XasWorks/Notos/Models/Modules/Bumper/FrontBumper.fcstd

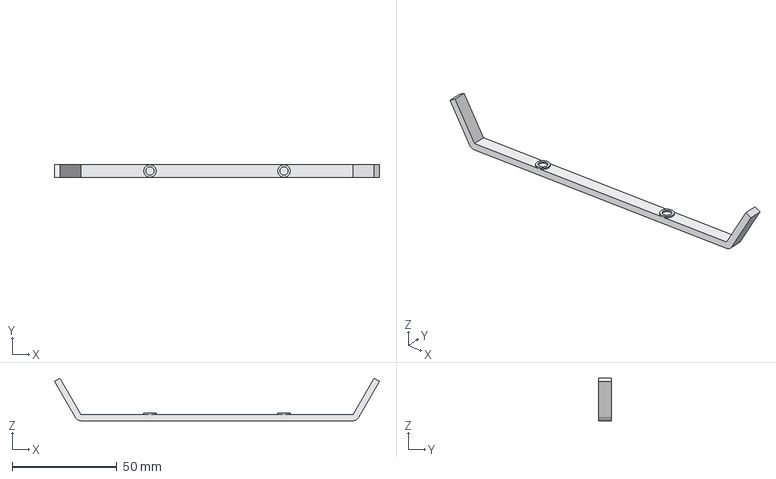
[picture p16: CAD file, 2017-02-04]
Models/Modules/Bumper/FrontBumper.fcstd
155.2 x 6.00 x 20.3 mm
