XasWorks/Notos/Models/BallSearch/Laser Side Mount.fcstd

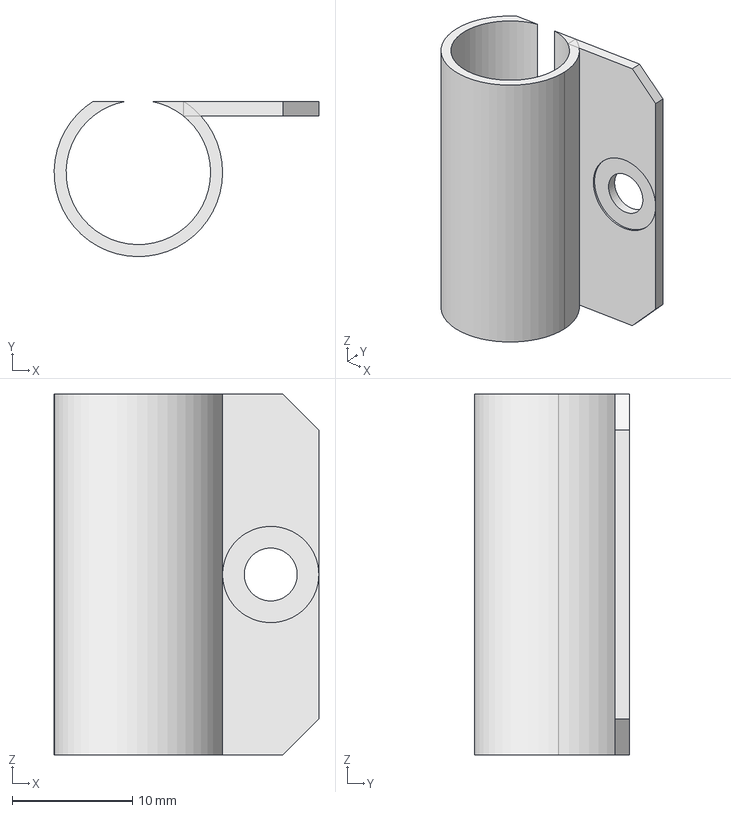
[picture p17: CAD file, 2017-04-10]
Models/BallSearch/Laser Side Mount.fcstd
22.0 x 12.9 x 30.0 mm
