XasWorks/Notos/Models/Modules/MultiSensorMount.fcstd

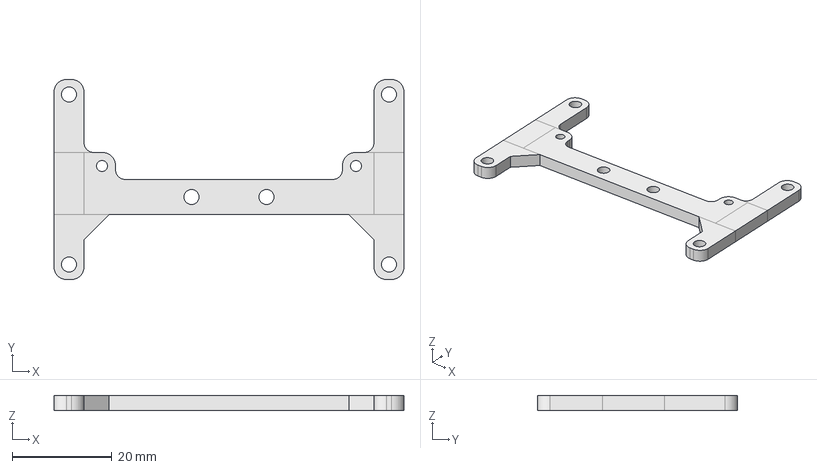
[picture p18: CAD file, 2017-03-13]
Models/Modules/MultiSensorMount.fcstd
70.0 x 40.0 x 3.00 mm
