XasWorks/Notos/Models/BallSearch/PhototransistorCover.fcstd

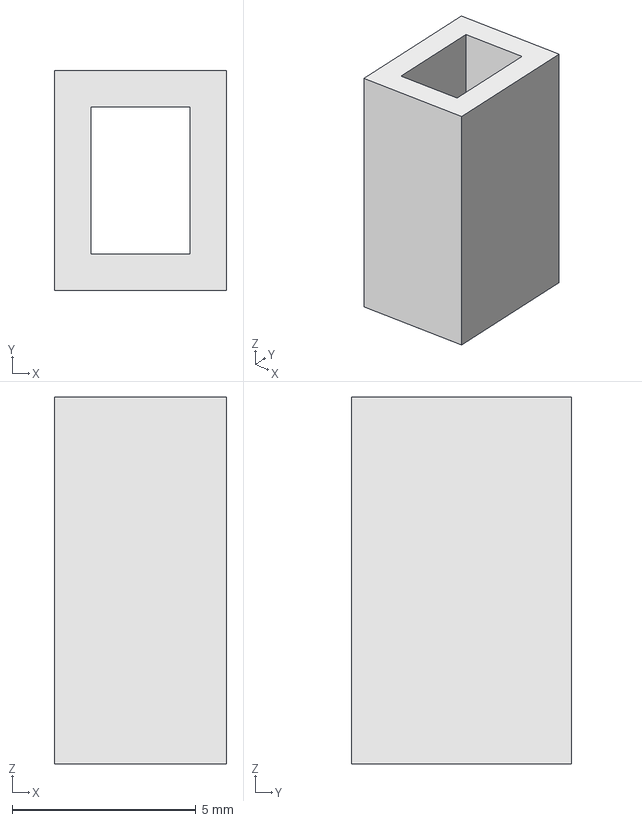
[picture p19: CAD file, 2017-04-10]
Models/BallSearch/PhototransistorCover.fcstd
4.70 x 6.00 x 10.0 mm
