XasWorks/Notos/Models/Modules/GroundDistanceSensor.fcstd

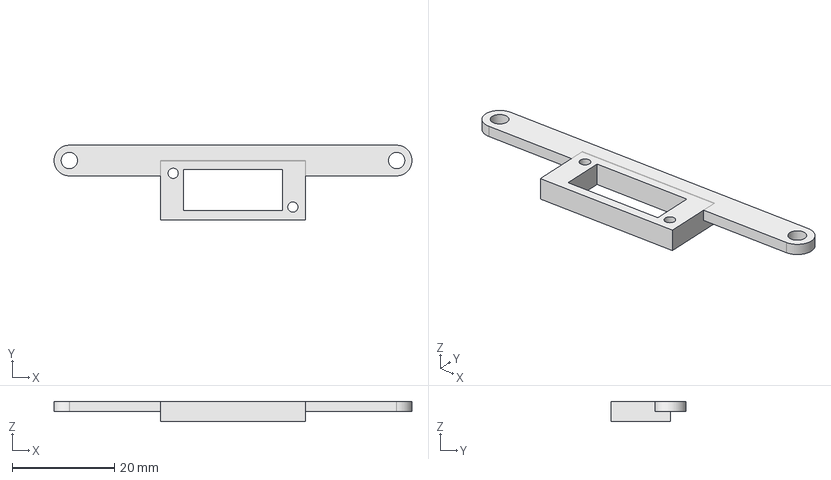
[picture p20: CAD file, 2017-02-13]
Models/Modules/GroundDistanceSensor.fcstd
70.0 x 14.6 x 4.00 mm
