XasWorks/Notos/Models/Modules/AnalogLineFollorSensors.fcstd

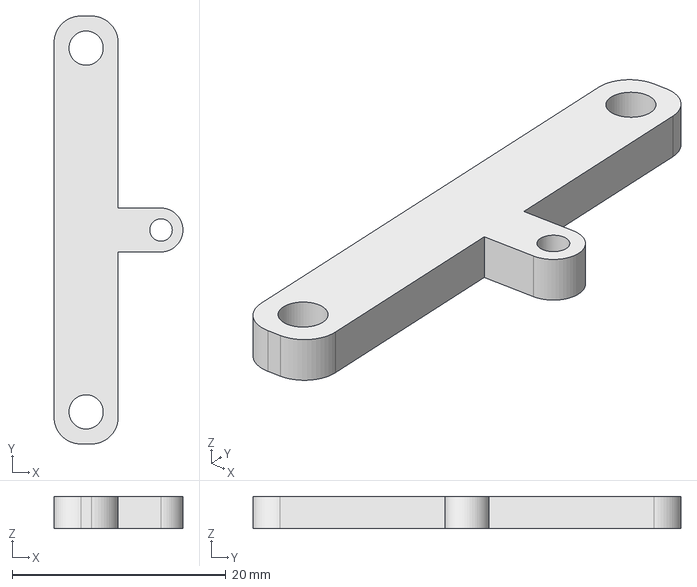
[picture p21: CAD file, 2017-02-13]
Models/Modules/AnalogLineFollorSensors.fcstd
12.0 x 40.0 x 3.00 mm
