XasWorks/Notos/Models/Modules/LineFollowSensors.fcstd

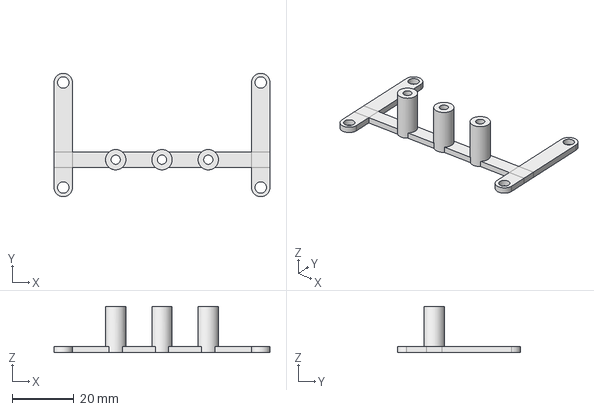
[picture p22: CAD file, 2017-02-04]
Models/Modules/LineFollowSensors.fcstd
70.0 x 40.0 x 15.0 mm
