XasWorks/Notos/Models/Modules/PartConnector.fcstd

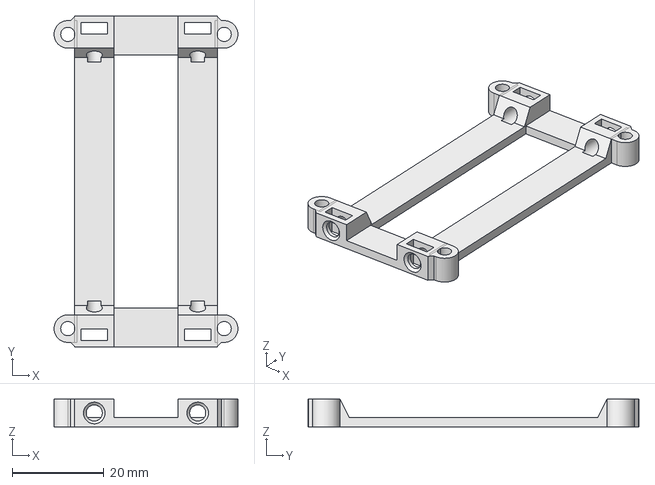
[picture p23: CAD file, 2016-12-08]
Models/Modules/PartConnector.fcstd
40.0 x 72.0 x 6.00 mm
