XasWorks/Notos/Models/Modules/Prototype_Connector.fcstd

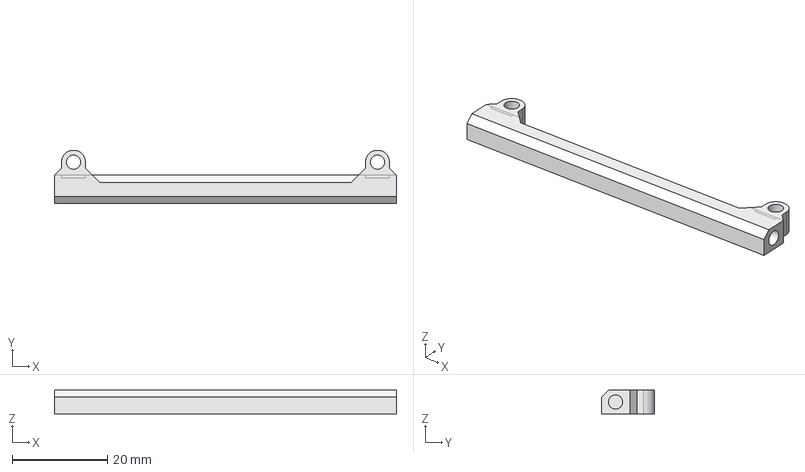
[picture p24: CAD file, 2016-12-08]
Models/Modules/Prototype_Connector.fcstd
72.0 x 11.2 x 5.00 mm
