XasWorks/Notos/Models/Mechanics/Mechanics.scad

include <../Values/Values.scad>

module idler_screw(backplate_aligned = true, shaftPlay = playTightFit) {

	totalHeadHeight = idlerScrewHeadHeight + playLooseFit;
	totalHeadDiameter = idlerScrewHeadDiameter + playLooseFit * 2;

	totalShaftDiameter = idlerScrewDiameter + shaftPlay * 2;

	translate([0, 0, (backplate_aligned) ? - totalHeadHeight : 0]) {

		// Shaft der Schraube
		translate([0, 0, totalHeadHeight - 0.0001 ]) cylinder(d = totalShaftDiameter, h = idlerScrewLength);
		// Angewinkeltes Zwischenstück zwischen Kopf und Shaft
		translate([0, 0, totalHeadHeight - idlerScrewHeadSlope - 0.02]) cylinder(r1 = totalHeadDiameter/2, r2 = totalShaftDiameter/2, h = idlerScrewHeadSlope + 0.04);
		// Kopf der Schraube
		cylinder(d = totalHeadDiameter, h = totalHeadHeight - idlerScrewHeadSlope);
	}
}

module idler_screw_nut() {
	difference() {
		cylinder(d = idlerNutDiameter + playTightFit * 2, h = idlerNutHeight);
		translate([0, 0, -0.1]) cylinder(d = idlerScrewDiameter - playTightFit * 2, h = idlerNutHeight + 0.2);
	}
}

module ball_bearing() {
	difference() {
		cylinder(d = ballBearingOuterDiameter + playTightFit * 2, h = ballBearingHeight);
		translate([0, 0, -0.1]) cylinder(d = ballBearingInnerDiameter - playTightFit * 2, h = ballBearingHeight + 0.2);
	}
}
