XasWorks/Notos/Models/Values/Backplate.scad

// -- Werte für die Backplate

// Dicke der Backplate
backplateThickness = 2;

// Wie viel Spielraum zwischen der BP und der Kette gelassen werden soll.
backplateTrackPlay = 2;

// Wie groß soll die Wand sein, welche die Mutter an der Frontplate umschließt
IdlerNutMountThickness = 1;

// Wie viel der BP soll unten "geschnitten" werden?
plateGroundClearance = 5;
