XasWorks/Notos/Models/Values/Plating.scad

// -- Werte für die Backplate

// Dicke der Backplate
backplateThickness = 2.5;
frontplateThickness = 2;
// Wie viel Spielraum zwischen der BP und der Kette gelassen werden soll.
plateTrackPlay = 2;
plateBearingRingHeight = 0.4;
plateBearingRingThickness = 1;

// Wie viel der BP soll unten "geschnitten" werden?
plateGroundClearance = 5;

// Stellen für die Platten-Verbinder
plateConnectors = [[-35, 30], [25, 30]];
// Höhe des Verbinders an der Backplate
backplateConnectorHeight = 5;
