XasWorks/Notos/EclipseWS/Notos_Main/Localcode/States/BallCapture.h

/*
 * BallCapture.h
 *
 *  Created on: 20.04.2017
 *      Author: xasin
 */

#ifndef LOCALCODE_STATES_BALLCAPTURE_H_
#define LOCALCODE_STATES_BALLCAPTURE_H_

#include "../../main.h"
#include <math.h>

#define FRONT_TO_CENTER 100

#define BALL_SEARCH_SPEED 3

#define CORNER_INSET		200	// Distance of the corner position from the course walls
#define CORNER_BUMP_LENGTH 	30	// The distance you have to move backwards to be roughly at the corner position, after bumping against the corner itself
#define CORNER_CHECK_LENGTH	150 // How much should the robot drive forwards before "calling it off"

#define WALL_ALIGNMENT_DISTANCE	100 // How much should the robot drive forwards to be sufficiently wall aligned

#define COURSE_SIZE_X 	(1200 - 2*FRONT_TO_CENTER)
#define COURSE_SIZE_Y 	(900  - 2*FRONT_TO_CENTER)

#define START_X	-150
#define START_Y	-450

namespace State {
namespace Ball {

struct Coords {
	float x;
	float y;
};


	void ballSearch();
}
}


#endif /* LOCALCODE_STATES_BALLCAPTURE_H_ */
