XasWorks/Notos/EclipseWS/PeripheralsBoard/Localcode/Packets.h

/*
 * Packets.h
 *
 *  Created on: 05.04.2017
 *      Author: xasin
 */

#ifndef PACKETS_H_
#define PACKETS_H_

enum PeripheralCommand : uint8_t {
	READ_LASER,
	SET_THRESHOLD,
	SET_ARM_MODE,
};

enum GrabbingArmModes : uint8_t {
	RETRACTED 		= 0,
	LOWERED_OPEN 	= 1,
	LOWERED_CLOSED 	= 2,
	RAISED_OPEN 	= 3,
	RAISED_CLOSED 	= 4,
};

struct LaserReadData {
	volatile uint8_t reflectance = 0;
	volatile int8_t hitStatus 	 = 0;
};

#endif /* PACKETS_H_ */
