XasWorks/Notos/EclipseWS/Notos_Main/Localcode/States/Intersection.h

/*
 * Intersection.h
 *
 *  Created on: Feb 18, 2017
 *      Author: xasin
 */

#ifndef LOCALCODE_STATES_INTERSECTION_H_
#define LOCALCODE_STATES_INTERSECTION_H_

#include "../Robot.h"

#define GREEN_THRESHOLD 80

#define SCAN_ANGLE		55

namespace State  {
namespace Intsec {

void runIntsec();

}
}


#endif /* LOCALCODE_STATES_INTERSECTION_H_ */
