XasWorks/Notos/EclipseWS/Notos_Main/Localcode/States/USB.h

/*
 * USB.h
 *
 *  Created on: 25.01.2017
 *      Author: xasin
 */

#ifndef LOCALCODE_STATES_USB_H_
#define LOCALCODE_STATES_USB_H_

#include "../../main.h"

namespace State {
namespace USB {

void simpleDebug();

}
}

#endif /* LOCALCODE_STATES_USB_H_ */
